LZP-2020-1-0200/Sensor-3D-control/stepper_driver/include/reporter.h

#ifndef REPORTER_H
#define REPORTER_H
#pragma once
#include <Arduino.h>

enum class ErrorSeverity {
	INFO,
	WARNING,
	ERROR,
	FATAL
};

void report(const __FlashStringHelper* msg, ErrorSeverity severity);
void report(const char* msg, ErrorSeverity severity);


#endif
