LZP-2020-1-0200/Sensor-3D-control/stepper_driver/include/modelData.h

#ifndef MANUFACTURER
#define MANUFACTURER "LU KFI"
#endif
#ifndef MODEL
// Mirorless assembly for microscopic imaging
#define MODEL "Mirrorless Assembly for Microscopic Imaging (MAMI)"
#endif
#ifndef SERIAL_NUMBER
#define SERIAL_NUMBER "0001"
#endif
#ifndef SOFTWARE_VERSION
#define SOFTWARE_VERSION "v1.0.1-alpha.0"
#endif
