LZP-2020-1-0200/Sensor-3D-control/stepper_driver/include/scpi2.h

#include <Arduino.h>

#define SCIPI_BUFFER_SIZE 127
#define SCIPI_MAX_ARGC 16


namespace scpi{
    

    class Command
    {
    public:
        struct ChildCMD
        {
            const char* const txt;
            Command* cmd;
            const size_t txtLen;
            // delete copy constructor and assignment operator
            ChildCMD(const ChildCMD& ccmd) : txt(ccmd.txt), cmd(ccmd.cmd), txtLen(ccmd.txtLen) { };
            ChildCMD& operator=(const ChildCMD&) = delete;
            ChildCMD(const char* const txt, Command* cmd)
                : txt(txt), cmd(cmd), txtLen(strlen(txt)){};
        };
    private:
        int (* const func)(int, char**)=nullptr;
        void (* const get)()=nullptr;
        
        int cmdInd(char*, int);
        const ChildCMD* const subcommands;
        const size_t childCMDCount;
    public:
        Command(int (* const func)(int, char**), void (* const get)(), const ChildCMD* const subCMD, int childCMDCount)
            : func(func), get(get),
              subcommands(subCMD), childCMDCount(childCMDCount){}
        template<size_t N>
        Command(int (* const func)(int, char**), void (* const get)(), const ChildCMD(&subCMD)[N] )
            : func(func), get(get),
              subcommands(subCMD), childCMDCount(N){}
        Command(int (* const func)(int, char**), void (* const get)())
            : func(func), get(get),
              subcommands(nullptr), childCMDCount(0){}
        Command(int (* const func)(int, char**))
            : func(func), get(nullptr),
              subcommands(nullptr), childCMDCount(0){}
        ~Command(){};
        // delete copy constructor and assignment operator
        Command(const Command& cmd) = delete;
        Command& operator=(const Command&) = delete;
        void dump(void) const;
        void parse(HardwareSerial&, char*);

    };

    class scpi2
    {
    private:
        HardwareSerial& serial;
        char input[SCIPI_BUFFER_SIZE+1];
        int inBufIndex=0;
        Command& cmd;
        
    public:
        scpi2(HardwareSerial& serial, Command& cmd): serial(serial), cmd(cmd){};
        ~scpi2();

        void update();
    };
}
