LZP-2020-1-0200/Sensor-3D-control/stepper_driver/include/vector.h

#ifndef VECTOR_H
#define VECTOR_H
class Vector{
public:
	int x;
	int y;
	int z;
	Vector(int x=0, int y=0, int z=0): x(x), y(y), z(z) {};
	Vector(Vector const& v): x(v.x), y(v.y), z(v.z) {};
	Vector operator+(Vector v);
	Vector operator+(int b);
	Vector operator-(Vector v);
	Vector operator-(int b);
	Vector operator*(int a);
	Vector operator/(int a);
	Vector& operator+=(int b);
	Vector& operator-=(int b);
	Vector& operator*=(int a);
	Vector& operator/=(int a);
};

Vector operator+(int b, Vector v);
Vector operator*(int a, Vector v);
#endif
